einfachuli/ZOE-Display/My Version V8.1/Bilder/Bildschirme/01 Ladeschirm_1.jpg

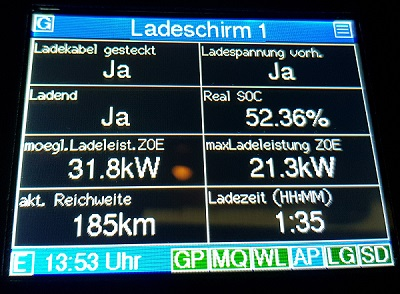
My Version V8.1/Bilder/Bildschirme/01 Ladeschirm_1.jpg
