einfachuli/ZOE-Display/My Version V8.1/Bilder/Bildschirme/02 Ladeschirm 2.jpg

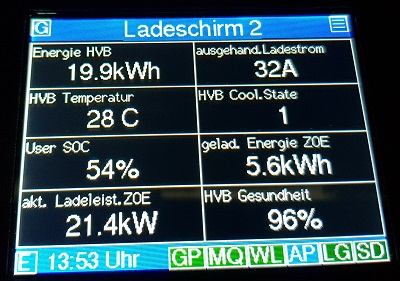
My Version V8.1/Bilder/Bildschirme/02 Ladeschirm 2.jpg
