einfachuli/ZOE-Display/My Version V8.1/Bilder/Bildschirme/07 Temperaturen.jpg

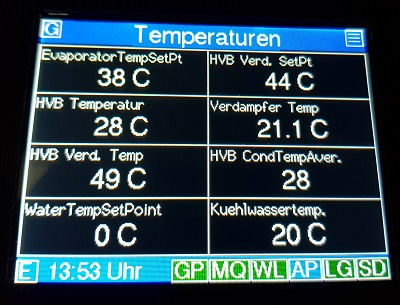
My Version V8.1/Bilder/Bildschirme/07 Temperaturen.jpg
