einfachuli/ZOE-Display/My Version V8.1/Bilder/Bildschirme/08 GPS.jpg

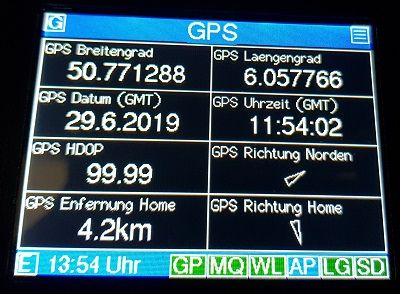
My Version V8.1/Bilder/Bildschirme/08 GPS.jpg
