einfachuli/ZOE-Display/My Version V8.1/Bilder/Bildschirme/11 Ladegrafik.jpg

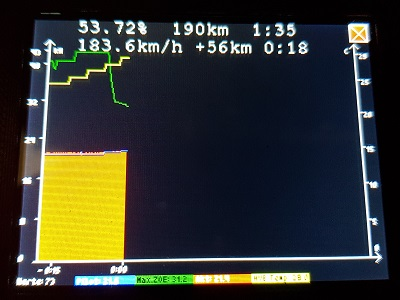
My Version V8.1/Bilder/Bildschirme/11 Ladegrafik.jpg
