einfachuli/ZOE-Display/My Version V8.1/Schaltplan_Seite_1.png

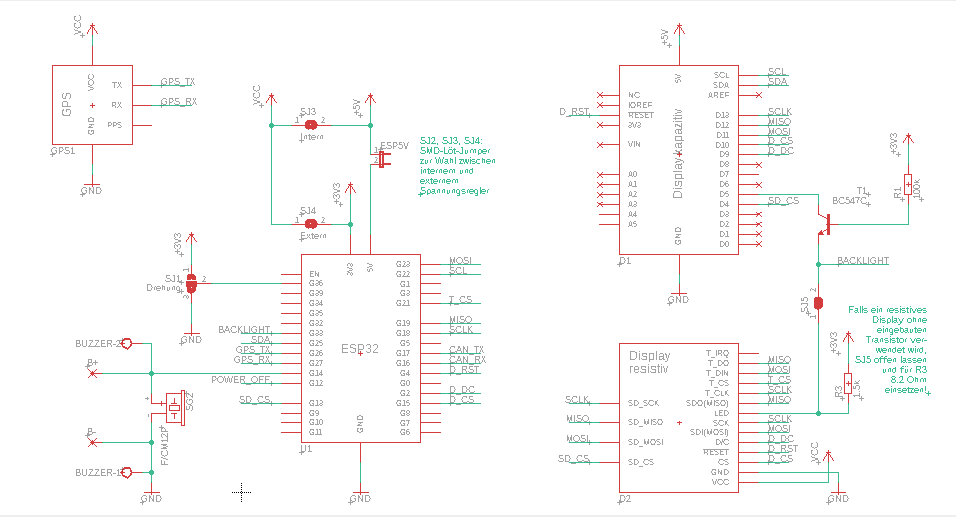
My Version V8.1/Schaltplan_Seite_1.png
