einfachuli/ZOE-Display/My Version V8.1/Schaltplan_Seite_2.png

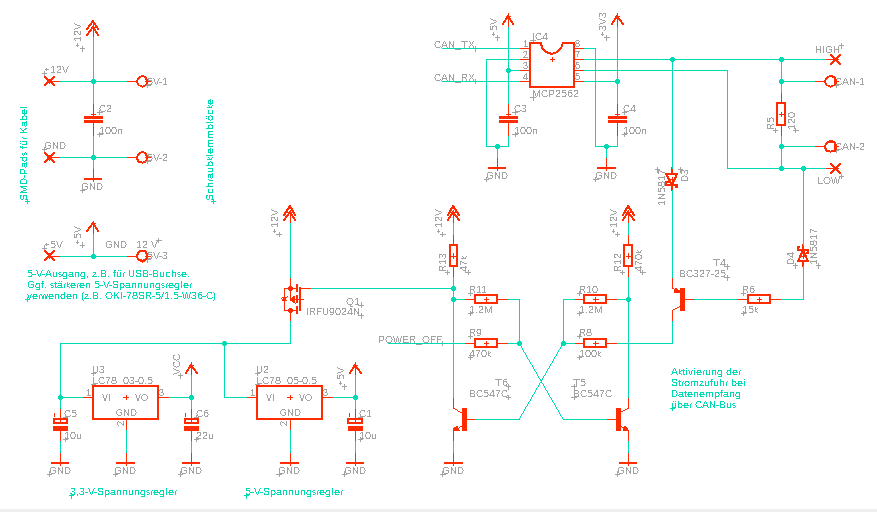
My Version V8.1/Schaltplan_Seite_2.png
