einfachuli/ZOE-Display/My Version V8.1/Bilder/Bildschirme/09 Debug.jpg

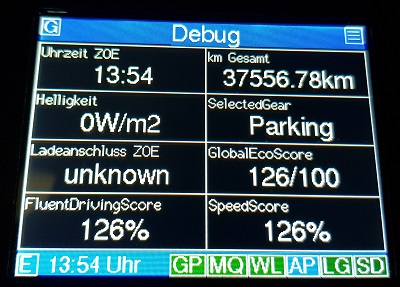
My Version V8.1/Bilder/Bildschirme/09 Debug.jpg
